gralco/ext-con-breakout-board/ext-con-breakout-board-sections.png

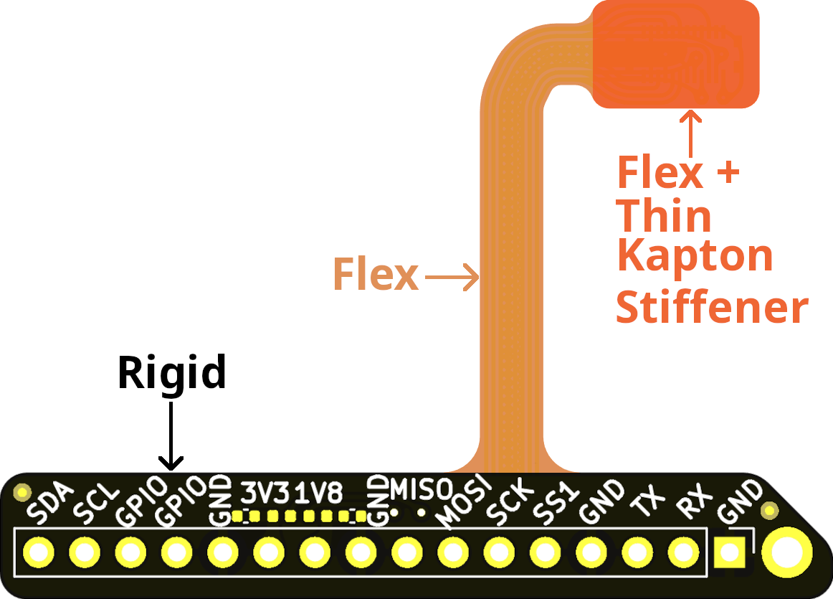
ext-con-breakout-board-sections.png
